pichenettes/ambika/voicecard/resources.h

// Copyright 2011 Emilie Gillet.
//
// Author: Emilie Gillet (emilie.o.gillet@gmail.com)
//
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
// -----------------------------------------------------------------------------
//
// Resources definitions.
//
// Automatically generated with:
// make resources


#ifndef VOICECARD_RESOURCES_H_
#define VOICECARD_RESOURCES_H_


#include "avrlib/base.h"

#include <avr/pgmspace.h>


#include "avrlib/resources_manager.h"

namespace ambika {

typedef uint8_t ResourceId;

extern const prog_char* const string_table[];

extern const prog_uint16_t* const lookup_table_table[];

extern const prog_uint8_t* const waveform_table[];

extern const prog_uint16_t lut_res_lfo_increments[] PROGMEM;
extern const prog_uint16_t lut_res_env_portamento_increments[] PROGMEM;
extern const prog_uint16_t lut_res_oscillator_increments[] PROGMEM;
extern const prog_uint16_t lut_res_fm_frequency_ratios[] PROGMEM;
extern const prog_uint16_t lut_res_vca_linearization[] PROGMEM;
extern const prog_uint16_t lut_res_cz_phase_reset[] PROGMEM;
extern const prog_uint8_t wav_res_formant_sine[] PROGMEM;
extern const prog_uint8_t wav_res_formant_square[] PROGMEM;
extern const prog_uint8_t wav_res_sine[] PROGMEM;
extern const prog_uint8_t wav_res_bandlimited_square_0[] PROGMEM;
extern const prog_uint8_t wav_res_bandlimited_square_1[] PROGMEM;
extern const prog_uint8_t wav_res_bandlimited_square_2[] PROGMEM;
extern const prog_uint8_t wav_res_bandlimited_square_3[] PROGMEM;
extern const prog_uint8_t wav_res_bandlimited_square_4[] PROGMEM;
extern const prog_uint8_t wav_res_bandlimited_square_5[] PROGMEM;
extern const prog_uint8_t wav_res_bandlimited_saw_0[] PROGMEM;
extern const prog_uint8_t wav_res_bandlimited_saw_1[] PROGMEM;
extern const prog_uint8_t wav_res_bandlimited_saw_2[] PROGMEM;
extern const prog_uint8_t wav_res_bandlimited_saw_3[] PROGMEM;
extern const prog_uint8_t wav_res_bandlimited_saw_4[] PROGMEM;
extern const prog_uint8_t wav_res_bandlimited_saw_5[] PROGMEM;
extern const prog_uint8_t wav_res_bandlimited_triangle_0[] PROGMEM;
extern const prog_uint8_t wav_res_bandlimited_triangle_3[] PROGMEM;
extern const prog_uint8_t wav_res_bandlimited_triangle_4[] PROGMEM;
extern const prog_uint8_t wav_res_bandlimited_triangle_5[] PROGMEM;
extern const prog_uint8_t wav_res_vowel_data[] PROGMEM;
extern const prog_uint8_t wav_res_distortion[] PROGMEM;
extern const prog_uint8_t wav_res_lfo_waveforms[] PROGMEM;
extern const prog_uint8_t wav_res_env_expo[] PROGMEM;
extern const prog_uint8_t wav_res_waves[] PROGMEM;
extern const prog_uint8_t wav_res_wavetables[] PROGMEM;
#define STR_RES_DUMMY 0  // dummy
#define LUT_RES_LFO_INCREMENTS 0
#define LUT_RES_LFO_INCREMENTS_SIZE 128
#define LUT_RES_ENV_PORTAMENTO_INCREMENTS 1
#define LUT_RES_ENV_PORTAMENTO_INCREMENTS_SIZE 128
#define LUT_RES_OSCILLATOR_INCREMENTS 2
#define LUT_RES_OSCILLATOR_INCREMENTS_SIZE 768
#define LUT_RES_FM_FREQUENCY_RATIOS 3
#define LUT_RES_FM_FREQUENCY_RATIOS_SIZE 25
#define LUT_RES_VCA_LINEARIZATION 4
#define LUT_RES_VCA_LINEARIZATION_SIZE 256
#define LUT_RES_CZ_PHASE_RESET 5
#define LUT_RES_CZ_PHASE_RESET_SIZE 4
#define WAV_RES_FORMANT_SINE 0
#define WAV_RES_FORMANT_SINE_SIZE 256
#define WAV_RES_FORMANT_SQUARE 1
#define WAV_RES_FORMANT_SQUARE_SIZE 256
#define WAV_RES_SINE 2
#define WAV_RES_SINE_SIZE 257
#define WAV_RES_BANDLIMITED_SQUARE_0 3
#define WAV_RES_BANDLIMITED_SQUARE_0_SIZE 257
#define WAV_RES_BANDLIMITED_SQUARE_1 4
#define WAV_RES_BANDLIMITED_SQUARE_1_SIZE 257
#define WAV_RES_BANDLIMITED_SQUARE_2 5
#define WAV_RES_BANDLIMITED_SQUARE_2_SIZE 257
#define WAV_RES_BANDLIMITED_SQUARE_3 6
#define WAV_RES_BANDLIMITED_SQUARE_3_SIZE 257
#define WAV_RES_BANDLIMITED_SQUARE_4 7
#define WAV_RES_BANDLIMITED_SQUARE_4_SIZE 257
#define WAV_RES_BANDLIMITED_SQUARE_5 8
#define WAV_RES_BANDLIMITED_SQUARE_5_SIZE 257
#define WAV_RES_BANDLIMITED_SQUARE_6 9
#define WAV_RES_BANDLIMITED_SQUARE_6_SIZE 257
#define WAV_RES_BANDLIMITED_SAW_0 10
#define WAV_RES_BANDLIMITED_SAW_0_SIZE 257
#define WAV_RES_BANDLIMITED_SAW_1 11
#define WAV_RES_BANDLIMITED_SAW_1_SIZE 257
#define WAV_RES_BANDLIMITED_SAW_2 12
#define WAV_RES_BANDLIMITED_SAW_2_SIZE 257
#define WAV_RES_BANDLIMITED_SAW_3 13
#define WAV_RES_BANDLIMITED_SAW_3_SIZE 257
#define WAV_RES_BANDLIMITED_SAW_4 14
#define WAV_RES_BANDLIMITED_SAW_4_SIZE 257
#define WAV_RES_BANDLIMITED_SAW_5 15
#define WAV_RES_BANDLIMITED_SAW_5_SIZE 257
#define WAV_RES_BANDLIMITED_SAW_6 16
#define WAV_RES_BANDLIMITED_SAW_6_SIZE 257
#define WAV_RES_BANDLIMITED_TRIANGLE_0 17
#define WAV_RES_BANDLIMITED_TRIANGLE_0_SIZE 257
#define WAV_RES__BANDLIMITED_TRIANGLE_0 18
#define WAV_RES__BANDLIMITED_TRIANGLE_0_SIZE 257
#define WAV_RES___BANDLIMITED_TRIANGLE_0 19
#define WAV_RES___BANDLIMITED_TRIANGLE_0_SIZE 257
#define WAV_RES_BANDLIMITED_TRIANGLE_3 20
#define WAV_RES_BANDLIMITED_TRIANGLE_3_SIZE 257
#define WAV_RES_BANDLIMITED_TRIANGLE_4 21
#define WAV_RES_BANDLIMITED_TRIANGLE_4_SIZE 257
#define WAV_RES_BANDLIMITED_TRIANGLE_5 22
#define WAV_RES_BANDLIMITED_TRIANGLE_5_SIZE 257
#define WAV_RES_BANDLIMITED_TRIANGLE_6 23
#define WAV_RES_BANDLIMITED_TRIANGLE_6_SIZE 257
#define WAV_RES_VOWEL_DATA 24
#define WAV_RES_VOWEL_DATA_SIZE 63
#define WAV_RES_DISTORTION 25
#define WAV_RES_DISTORTION_SIZE 256
#define WAV_RES_LFO_WAVEFORMS 26
#define WAV_RES_LFO_WAVEFORMS_SIZE 2
#define WAV_RES_ENV_EXPO 27
#define WAV_RES_ENV_EXPO_SIZE 257
#define WAV_RES_WAVES 28
#define WAV_RES_WAVES_SIZE 10320
#define WAV_RES_WAVETABLES 29
#define WAV_RES_WAVETABLES_SIZE 288
typedef avrlib::ResourcesManager<
    ResourceId,
    avrlib::ResourcesTables<
        string_table,
        lookup_table_table> > ResourcesManager; 

}  // namespace ambika

#endif  // VOICECARD_RESOURCES_H_
