pichenettes/ambika/controller/multi.h

// Copyright 2011 Emilie Gillet.
//
// Author: Emilie Gillet (emilie.o.gillet@gmail.com)
//
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
// -----------------------------------------------------------------------------
//
// "MultiData" is the dumb data structure storing the global settings.
// "Multi" is the root synthesis engine.

#ifndef CONTROLLER_MULTI_H_
#define CONTROLLER_MULTI_H_

#include "avrlib/base.h"

#include "controller/controller.h"
#include "controller/part.h"

namespace ambika {
  
struct KnobAssignment {
  uint8_t part;
  uint8_t parameter;
  uint8_t instance;
};

struct PartMapping {
  uint8_t midi_channel;
  uint8_t keyrange_low;
  uint8_t keyrange_high;
  uint8_t voice_allocation;
  
  inline uint8_t receive_channel(uint8_t channel) const {
    return !midi_channel || (channel + 1 == midi_channel);
  }
  
  inline uint8_t accept_note(uint8_t note) const {
    if (keyrange_low <= keyrange_high) {
      return (note >= keyrange_low && note <= keyrange_high);
    } else {
      return note <= keyrange_high || note >= keyrange_low;
    }
  }
  
  inline uint8_t accept_channel_note(uint8_t channel, uint8_t note) const {
    return receive_channel(channel) && accept_note(note);
  }
  
  inline uint8_t tx_channel() const {
    return midi_channel == 0 ? 0 : midi_channel - 1;
  }
};

struct MultiData {
  // Offset: 0-24
  PartMapping part_mapping_[kNumParts];
  
  // Offset: 24-28
  uint8_t clock_bpm;
  uint8_t clock_groove_template;
  uint8_t clock_groove_amount;
  uint8_t clock_release;
  
  // Offset: 28-52
  KnobAssignment knob_assignment[8];
  
  // Offset: 52-56
  uint8_t padding2[4];
};

typedef MultiData PROGMEM prog_MultiData;

enum MultiParameter {
  PRM_MULTI_MIDI_CHANNEL,
  PRM_MULTI_KEYRANGE_LOW,
  PRM_MULTI_KEYRANGE_HIGH,
  PRM_MULTI_VOICE_ALLOCATION,
  
  PRM_MULTI_CLOCK_BPM = 24,
  PRM_MULTI_CLOCK_GROOVE_TEMPLATE = 25,
  PRM_MULTI_CLOCK_GROOVE_AMOUNT = 26,
  PRM_MULTI_CLOCK_LATCH = 27,
};

static const uint8_t kNumStepsInGroovePattern = 16;
static const uint8_t kNumTicksPerStep = 6;

class Multi {
 public:
  Multi() { }
  static void Init(bool force_reset);
  
  static void InitSettings(InitializationMode mode);
  
  static void StartNote(uint8_t note) {
    if (!running_) {
      Start();
    }
    for (uint8_t i = 0; i < kNumParts; ++i) {
      parts_[i].NoteOn(note, 0x64);
    }
  }
  
  static void StopNote(uint8_t note) {
    for (uint8_t i = 0; i < kNumParts; ++i) {
      parts_[i].NoteOff(note);
    }
  }
  
  static void NoteOn(uint8_t channel, uint8_t note, uint8_t velocity) {
    // If no note has been played for a while, reset the sequencer and
    // arpeggiator to the first step.
    if (!running_) {
      Start();
    }
    for (uint8_t i = 0; i < kNumParts; ++i) {
      if (data_.part_mapping_[i].accept_channel_note(channel, note)) {
        parts_[i].NoteOn(note, velocity);
      }
    }
  }
  static void NoteOff(uint8_t channel, uint8_t note, uint8_t velocity) {
    for (uint8_t i = 0; i < kNumParts; ++i) {
      if (data_.part_mapping_[i].accept_channel_note(channel, note)) {
        parts_[i].NoteOff(note);
      }
    }
  }
  static void ControlChange(
      uint8_t channel,
      uint8_t controller,
      uint8_t value) {
    for (uint8_t i = 0; i < kNumParts; ++i) {
      if (data_.part_mapping_[i].receive_channel(channel)) {
        parts_[i].ControlChange(controller, value);
      }
    }
  }
  static void PitchBend(uint8_t channel, uint16_t pitch_bend) {
    for (uint8_t i = 0; i < kNumParts; ++i) {
      if (data_.part_mapping_[i].receive_channel(channel)) {
        parts_[i].PitchBend(pitch_bend);
      }
    }
  }
  static void Aftertouch(uint8_t channel, uint8_t note, uint8_t velocity) {
    for (uint8_t i = 0; i < kNumParts; ++i) {
      if (data_.part_mapping_[i].accept_channel_note(channel, note)) {
        parts_[i].Aftertouch(note, velocity);
      }
    }
  }
  static void Aftertouch(uint8_t channel, uint8_t velocity) {
    for (uint8_t i = 0; i < kNumParts; ++i) {
      if (data_.part_mapping_[i].receive_channel(channel)) {
        parts_[i].Aftertouch(velocity);
      }
    }
  }
  static void AllSoundOff(uint8_t channel) {
    for (uint8_t i = 0; i < kNumParts; ++i) {
      if (data_.part_mapping_[i].receive_channel(channel)) {
        parts_[i].AllSoundOff();
      }
    }
  }
  static void ResetAllControllers(uint8_t channel) {
    for (uint8_t i = 0; i < kNumParts; ++i) {
      if (data_.part_mapping_[i].receive_channel(channel)) {
        parts_[i].ResetAllControllers();
      }
    }
  }
  static void AllNotesOff(uint8_t channel) {
    for (uint8_t i = 0; i < kNumParts; ++i) {
      if (data_.part_mapping_[i].receive_channel(channel)) {
        parts_[i].AllNotesOff();
      }
    }
  }
  static void OmniModeOff(uint8_t channel) {
    for (uint8_t i = 0; i < kNumParts; ++i) {
      if (data_.part_mapping_[i].receive_channel(channel)) {
        data_.part_mapping_[i].midi_channel = channel + 1;
      }
    }
  }
  static void OmniModeOn(uint8_t channel) {
    for (uint8_t i = 0; i < kNumParts; ++i) {
      if (data_.part_mapping_[i].receive_channel(channel)) {
        data_.part_mapping_[i].midi_channel = 0;
      }
    }
  }
  static void MonoModeOn(uint8_t channel, uint8_t num_channels) {
    for (uint8_t i = 0; i < kNumParts; ++i) {
      if (data_.part_mapping_[i].receive_channel(channel)) {
        parts_[i].MonoModeOn(num_channels);
      }
    }
  }
  static void PolyModeOn(uint8_t channel) {
    for (uint8_t i = 0; i < kNumParts; ++i) {
      if (data_.part_mapping_[i].receive_channel(channel)) {
        parts_[i].PolyModeOn();
      }
    }
  }
  static void Reset() {
    for (uint8_t i = 0; i < kNumParts; ++i) {
      parts_[i].Reset();
    }
  }
  static void Clock();
  static void Start();
  static void Stop();
  static void Continue() {
    Start();
  }
  
  static void Tick() {
    ++clock_counter_;
    ++lfo_refresh_counter_;
    if (clock_counter_ >= tick_duration_) {
      ++num_clock_events_;
      clock_counter_ = 0;
    }
  }
  
  static void SetValue(uint8_t address, uint8_t value);
  static inline uint8_t GetValue(uint8_t address) {
    uint8_t* bytes = static_cast<uint8_t*>(static_cast<void*>(&data_));
    return bytes[address];
  }
  
  static void UpdateClocks();
  
  static Part* mutable_part(uint8_t i) { return &parts_[i]; }
  static const Part& part(uint8_t i) { return parts_[i]; }
  
  static MultiData* mutable_data() { return &data_; }
  static const MultiData& data() { return data_; }
  static const uint8_t* raw_data() {
    return static_cast<const uint8_t*>(static_cast<const void*>(&data_));
  }
  static uint8_t* mutable_raw_data() { 
    return static_cast<uint8_t*>(static_cast<void*>(&data_));
  }
  
  static uint8_t internal_clock() { return data_.clock_bpm >= 40; }

  static uint8_t SolveAllocationConflicts(uint8_t constraint);
  static void AssignVoicesToParts();
  
  static uint8_t part_channel(Part* part) {
    for (uint8_t i = 0; i < kNumParts; ++i) {
      if (&parts_[i] == part) {
        return data_.part_mapping_[i].tx_channel();
      }
    }
    return 0;
  }
  
  static uint8_t step() { return step_count_; }
  static uint8_t running() { return running_; }
  static void Touch();
  
  static inline uint8_t flags() {
    uint8_t result = flags_;
    for (uint8_t i = 0; i < kNumParts; ++i) {
      result |= parts_[i].flags();
    }
    return result;
  }
  
  inline void ClearFlag(uint8_t flag) {
    flags_ &= ~flag;
    for (uint8_t i = 0; i < kNumParts; ++i) {
      parts_[i].ClearFlag(flag);
    }
  }
  
 private:
  static void ComputeInternalClockOverflowsTable();
  
  // Incremented at 39kHz
  static uint16_t clock_counter_;
  static uint16_t lfo_refresh_counter_;
  // Incremented at 39kHz / 40
  static uint8_t lfo_refresh_cycle_;
  static volatile uint8_t num_clock_events_;

  // Duration of a clock tick, in 39kHz increments.
  static uint16_t tick_duration_;
  // Incremented at each clock tick, reset after 6 ticks.
  static uint8_t tick_count_;
  // Incremented every 6 tick.
  static uint8_t step_count_;
  // Incremented at each clock tick if no key is pressed.
  static uint8_t idle_ticks_;
  // Whether the clock is started.
  static uint8_t running_;
  // This list of tick durations is computed from the BPM and the groove
  // template.
  static uint16_t tick_duration_table_[kNumStepsInGroovePattern];
  

  static MultiData data_;
  static Part parts_[kNumParts];
  static uint8_t flags_;
  
  DISALLOW_COPY_AND_ASSIGN(Multi);
};

extern Multi multi;

}  // namespace ambika

#endif  // CONTROLLER_MULTI_H_
