pichenettes/ambika/controller/storage.cc

// Copyright 2011 Emilie Gillet.
//
// Author: Emilie Gillet (emilie.o.gillet@gmail.com)
//
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
// -----------------------------------------------------------------------------
//
// Patch storage and SysEx transfer.

#include "controller/storage.h"

#include <avr/eeprom.h>

#include "avrlib/op.h"
#include "avrlib/string.h"

#include "controller/display.h"
#include "controller/midi_dispatcher.h"
#include "controller/multi.h"
#include "controller/system_settings.h"
#include "controller/ui.h"

namespace ambika {


static const uint32_t kRiffTag = FourCC<'R', 'I', 'F', 'F'>::value;
static const uint32_t kFormatTag = FourCC<'M', 'B', 'K', 'S'>::value;
static const uint32_t kNameTag = FourCC<'n', 'a', 'm', 'e'>::value;
static const uint32_t kObjectTag = FourCC<'o', 'b', 'j', ' '>::value;

using namespace avrlib;

static const prog_char sysex_header[] PROGMEM = {
  0xf0,  // <SysEx>
  0x00, 0x21, 0x02,  // Mutable instruments manufacturer id.
  0x00, 0x04,  // Product ID for Ambika-6.
};

/* static */
Filesystem Storage::fs_;

/* static */
File Storage::file_;

/* static */
uint8_t* Storage::buffer_;

/* static */
uint16_t Storage::sysex_rx_bytes_received_;

/* static */
uint8_t Storage::sysex_rx_checksum_;

/* static */
uint8_t Storage::sysex_rx_state_;

/* static */
uint16_t Storage::sysex_rx_expected_size_;

/* static */
uint8_t Storage::sysex_rx_command_[2];

/* static */
char Storage::tmp_buffer_[64];

/* static */
uint8_t Storage::version_[kNumVoices * 3 + 1];

/* static */
void Storage::Init() {
  buffer_ = fs_.buffer();
}

/* static */
uint8_t Storage::Checksum(const void* data, uint8_t size) {
  uint8_t s = 0;
  const uint8_t* d = static_cast<const uint8_t*>(data);
  while (size--) {
    s += *d++;
  }
  return s;
}

/* static */
void Storage::WriteMultiToEeprom() {
  uint16_t address = 0;
  for (uint8_t i = 0; i < kNumParts; ++i) {
    EepromWrite(
        multi.part(i).raw_data(),
        sizeof(PartData),
        &address);
    EepromWrite(
        multi.part(i).raw_patch_data(),
        sizeof(Patch),
        &address);
  }
  EepromWrite(multi.raw_data(), sizeof(MultiData), &address);
}

/* static */
uint8_t Storage::LoadMultiFromEeprom() {
  uint16_t address = 0;
  uint8_t success = 1;
  for (uint8_t i = 0; i < kNumParts; ++i) {
    success = success && Storage::EepromRead(
        multi.mutable_part(i)->mutable_raw_data(),
        sizeof(PartData),
        &address);
    success = success && Storage::EepromRead(
        multi.mutable_part(i)->mutable_raw_patch_data(),
        sizeof(Patch),
        &address);
  }
  success = success && Storage::EepromRead(
      multi.mutable_raw_data(),
      sizeof(MultiData),
      &address);
  return success;
}


/* static */
void Storage::EepromWrite(const void* data, uint8_t size, uint16_t* offset) {
  eeprom_write_block(const_cast<void*>(data), (void*)(*offset), size);
  *offset += size;
  eeprom_write_byte((uint8_t*)(*offset), Storage::Checksum(data, size));
  *offset += 1;
}

/* static */
uint8_t Storage::EepromRead(
    void* data,
    uint8_t size,
    uint16_t* offset) {
  eeprom_read_block(data, (void*)(*offset), size);
  *offset += size;
  uint8_t expected_checksum = eeprom_read_byte((uint8_t*)(*offset));
  *offset += 1;
  return Storage::Checksum(data, size) == expected_checksum;
}

/* static */
uint8_t Storage::object_size(const StorageLocation& location) {
  switch (location.object) {
    case STORAGE_OBJECT_PATCH:
      return sizeof(Patch);
      
    case STORAGE_OBJECT_SEQUENCE:
      return 72;
      
    case STORAGE_OBJECT_PART:
      return sizeof(PartData);
      
    case STORAGE_OBJECT_MULTI:
      return sizeof(MultiData);
  }
  return 0;
}

/* static */
uint16_t Storage::riff_size(const StorageLocation& location) {
  switch (location.object) {
    case STORAGE_OBJECT_MULTI:
      return (sizeof(Patch) + 12 + sizeof(PartData) + 12) * kNumParts + \
          sizeof(MultiData) + 12;

    case STORAGE_OBJECT_PROGRAM:
      return sizeof(Patch) + 12 + sizeof(PartData) + 12;
    
    default:
      return object_size(location) + 12;
  }
  return 0;
}

/* static */
const uint8_t* Storage::object_data(const StorageLocation& location) {
  switch (location.object) {
    case STORAGE_OBJECT_PATCH:
      return multi.part(location.part).raw_patch_data();
      
    case STORAGE_OBJECT_SEQUENCE:
      return multi.part(location.part).raw_sequence_data();
      
    case STORAGE_OBJECT_PART:
      return multi.part(location.part).raw_data();
      
    case STORAGE_OBJECT_MULTI:
      return multi.raw_data();
  }
  return NULL;
}

/* static */
uint8_t* Storage::mutable_object_data(const StorageLocation& location) {
  switch (location.object) {
    case STORAGE_OBJECT_PATCH:
      return multi.mutable_part(location.part)->mutable_raw_patch_data();
      
    case STORAGE_OBJECT_SEQUENCE:
      return multi.mutable_part(location.part)->mutable_raw_sequence_data();
      
    case STORAGE_OBJECT_PART:
      return multi.mutable_part(location.part)->mutable_raw_data();
      
    case STORAGE_OBJECT_MULTI:
      return multi.mutable_raw_data();
  }
  return NULL;
}

/* static */
uint8_t Storage::has_user_changes(const StorageLocation& location) {
  if (location.object == STORAGE_OBJECT_MULTI) {
    return multi.flags() & FLAG_HAS_USER_CHANGE;
  } else {
    return multi.part(location.part).flags() & FLAG_HAS_USER_CHANGE;
  }
}

/* static */
FilesystemStatus Storage::Snapshot(const StorageLocation& location) {
  StorageLocation l = location;
  uint8_t version = version_[location.index()];
  l.slot = version;
  Save(STORAGE_HISTORY, l);
  
  // Create a gap in the version number sequence to prevent forwarding.
  ++version;
  l.slot = version;
  char* forward_version_name = GetFileName(STORAGE_HISTORY, l);
  {
    scoped_resource<SdCardSession> session;
    InvalidatePendingSysExTransfer();
    fs_.Unlink(forward_version_name);
  }
  version_[location.index()] = version;
}

/* static */
FilesystemStatus Storage::PreviousVersion(const StorageLocation& location) {
  StorageLocation l = location;
  uint8_t version = version_[location.index()] - 1;
  l.slot = version;
  FilesystemStatus status = Load(STORAGE_HISTORY, l, 1);
  if (status == FS_OK) {
    version_[location.index()] = version;
  }
  return status;
}

/* static */
FilesystemStatus Storage::NextVersion(const StorageLocation& location) {
  StorageLocation l = location;
  uint8_t version = version_[location.index()] + 1;
  l.slot = version;
  FilesystemStatus status = Load(STORAGE_HISTORY, l, 1);
  if (status == FS_OK) {
    version_[location.index()] = version;
  }
  return status;
}

/* static */
void Storage::ForEachObject(
    const StorageLocation& location,
    ObjectFn object_fn) {
  StorageLocation destination = location;
  destination.alias = 0;
  switch(destination.object) {
    case STORAGE_OBJECT_PATCH:
    case STORAGE_OBJECT_SEQUENCE:
    case STORAGE_OBJECT_PART:
      (*object_fn)(destination);
      break;
      
    case STORAGE_OBJECT_PROGRAM:
      destination.object = STORAGE_OBJECT_PATCH;
      (*object_fn)(destination);
      destination.object = STORAGE_OBJECT_PART;
      (*object_fn)(destination);
      break;
      
    case STORAGE_OBJECT_MULTI:
      (*object_fn)(destination);
      for (uint8_t i = 0; i < kNumParts; ++i) {
        destination.part = i;
        destination.alias = i + 1;
        destination.object = STORAGE_OBJECT_PATCH;
        (*object_fn)(destination);
        destination.object = STORAGE_OBJECT_PART;
        (*object_fn)(destination);
      }
      break;
  }
}

/* static */
void Storage::ReadObject(const StorageLocation& location) {
  uint8_t* data = mutable_object_data(location);
  uint8_t size = object_size(location);
  if (size) {
    memcpy(data, buffer_, size);
  }
}

/* static */
void Storage::TouchObject(const StorageLocation& location) {
  // Recompute the dependent variables and update the voicecard. Mark that the
  // object is freshly loaded and has received no user changes.
  switch (location.object) {
    case STORAGE_OBJECT_PATCH:
      multi.mutable_part(location.part)->TouchPatch();
      break;

    case STORAGE_OBJECT_PART:
    case STORAGE_OBJECT_SEQUENCE:
      multi.mutable_part(location.part)->Touch();
      break;
    
    case STORAGE_OBJECT_MULTI:
      multi.Touch();
      break;
  }
}

/* static */
void Storage::SysExSendObject(const StorageLocation& location) {
  SysExSendRaw(
      location.object + 1,
      location.alias,
      object_data(location),
      object_size(location),
      false);
}

/* static */
void Storage::SysExSendRaw(
    uint8_t command,
    uint8_t argument,
    const uint8_t* data,
    uint8_t size,
    bool send_address) {
  midi_dispatcher.Flush();
  for (uint8_t i = 0; i < sizeof(sysex_header); ++i) {
    midi_dispatcher.SendBlocking(pgm_read_byte(sysex_header + i));
  }
  midi_dispatcher.SendBlocking(command);
  midi_dispatcher.SendBlocking(argument);
  // Outputs the data.
  uint8_t checksum = 0;
  if (send_address) {
    Word address;
    address.value = (uint16_t)(void*)(data);
    checksum += address.bytes[0];
    checksum += address.bytes[1];
    midi_dispatcher.SendBlocking(U8ShiftRight4(address.bytes[0]));
    midi_dispatcher.SendBlocking(address.bytes[0] & 0x0f);
    midi_dispatcher.SendBlocking(U8ShiftRight4(address.bytes[1]));
    midi_dispatcher.SendBlocking(address.bytes[1] & 0x0f);
  }
  for (uint8_t i = 0; i < size; ++i) {
    checksum += data[i];
    midi_dispatcher.SendBlocking(U8ShiftRight4(data[i]));
    midi_dispatcher.SendBlocking(data[i] & 0x0f);
  }
  // Outputs a checksum.
  midi_dispatcher.SendBlocking(U8ShiftRight4(checksum));
  midi_dispatcher.SendBlocking(checksum & 0x0f);

  // End of SysEx block.
  midi_dispatcher.SendBlocking(0xf7);
  midi_dispatcher.Flush();
}

/* static */
void Storage::RIFFWriteObject(const StorageLocation& location) {
  const uint8_t* data = object_data(location);
  uint8_t size = object_size(location);
  
  LongWord w;
  uint16_t written;

  // Write the RIFF header.
  w.value = kObjectTag;
  file_.Write(w.bytes, 4, &written);
  w.value = size + 4;
  file_.Write(w.bytes, 4, &written);
  // Write the position words.
  w.value = 0;
  w.bytes[0] = location.object + 1;
  w.bytes[1] = location.alias;
  file_.Write(w.bytes, 4, &written);
  
  // Write the data.
  file_.Write(data, size, &written);
}

/* static */
FilesystemStatus Storage::Load(
    StorageDir type,
    const StorageLocation& location,
    uint8_t load_contents) {
  {
    scoped_resource<SdCardSession> session;

    FilesystemStatus s;
    char* name = GetFileName(type, location);
  
    file_.Close();
    InvalidatePendingSysExTransfer();
  
    s = file_.Open(name, FA_READ | FA_OPEN_EXISTING, kFsInitTimeout);
    if (s != FS_OK) {
      return s;
    }
  
    LongWord id;
    LongWord size;
    uint16_t read;
  
    file_.Read(id.bytes, 4, &read);
    if (id.value != kRiffTag) {
      file_.Close();
      return FS_BAD_FILE_FORMAT;
    }
    // Skip the size.
    file_.Read(size.bytes, 4, &read);
    file_.Read(id.bytes, 4, &read);
    if (id.value != kFormatTag) {
      file_.Close();
      return FS_BAD_FILE_FORMAT;
    }
  
    while (!file_.eof()) {
      file_.Read(id.bytes, 4, &read);
      file_.Read(size.bytes, 4, &read);
      uint8_t skip_data = 1;
    
      if (id.value == kObjectTag && load_contents) {
        file_.Read(id.bytes, 4, &read);
        StorageLocation destination;
        destination.object = static_cast<StorageObject>(id.bytes[0] - 1);
        destination.part = id.bytes[1] == 0 ? location.part : (id.bytes[1] - 1);
      
        uint8_t expected_size = object_size(destination);
        if (expected_size == size.value - 4) {
          uint8_t* data = mutable_object_data(destination);
          file_.Read(data, expected_size, &read);
          skip_data = 0;
        }
      } else if (id.value == kNameTag && location.name) {
        file_.Read(location.name, size.value, &read);
        skip_data = 0;
      }
      if (skip_data) {
        file_.Seek(file_.tell() + size.value);
      }
    }

    file_.Close();
  }
  
  // Refresh all datastructures.
  if (load_contents) {
    ForEachObject(location, TouchObject);
  }

  return FS_OK;
}

/* static */
FilesystemStatus Storage::Save(
    StorageDir type,
    const StorageLocation& location) {
  scoped_resource<SdCardSession> session;
  
  FilesystemStatus s;
  char* name = GetFileName(type, location);

  file_.Close();
  InvalidatePendingSysExTransfer();
  
  // Create a backup of the older version.
  if (type == STORAGE_CLIPBOARD ||
      (type == STORAGE_BANK && system_settings.data().autobackup)) {
    char* backup_name = tmp_buffer_ + 32;
    strcpy(backup_name, name);
    backup_name[strlen(backup_name) - 3] = '~';
    
    // Remove the old backup.
    fs_.Unlink(backup_name);
    
    // Rename current version with the backup name.
    fs_.Rename(name, backup_name);
  }
  
  // Attempt to open.
  s = file_.Open(name, FA_WRITE | FA_CREATE_ALWAYS, kFsInitTimeout);
  if (s == FS_PATH_NOT_FOUND) {
    fs_.Mkdirs(name);
    s = file_.Open(name, FA_WRITE | FA_CREATE_ALWAYS, kFsInitTimeout);
  }
  
  // There's nothing we can do if Open failed at this stage.
  if (s != FS_OK) {
    return s;
  }
  
  LongWord w;
  uint16_t written;
  
  // RIFF header.
  w.value = kRiffTag;
  file_.Write(w.bytes, 4, &written);
  w.value = 4 + 24 + riff_size(location);
  file_.Write(w.bytes, 4, &written);
  w.value = kFormatTag;
  file_.Write(w.bytes, 4, &written);
  
  // NAME block.
  w.value = kNameTag;
  file_.Write(w.bytes, 4, &written);
  w.value = 16;
  file_.Write(w.bytes, 4, &written);
  file_.Write(location.name, 16, &written);

  // Write subchunks.
  ForEachObject(location, &RIFFWriteObject);
  
  file_.Close();
  return FS_OK;
}

/* static */
char* Storage::GetFileName(StorageDir type, const StorageLocation& location) {
  char* p = tmp_buffer_;

  // Root.
  *p++ = '/';

  // Object name.
  ResourcesManager::LoadStringResource(STR_RES_PATCH + location.object, p, 32);
  p += strlen(p);
  
  // Path.
  if (type == STORAGE_CLIPBOARD || type == STORAGE_PREVIOUS_CLIPBOARD) {
    strcat_P(p, PSTR("/CLIPBRD/CLIPBRD"));
    p += strlen(p);
  } else if (type == STORAGE_HISTORY) {
    strcat_P(p, PSTR("/HISTORY/"));
    p += strlen(p);
    if (location.object != STORAGE_OBJECT_MULTI) {
      *p++ = '0' + (location.part);
      *p++ = '/';
    }
  } else if (type == STORAGE_BANK) {
    strcat_P(p, PSTR("/BANK/"));
    p += strlen(p);
    *p++ = 'A' + (location.bank);
    *p++ = '/';
  }
  
  // Name.
  if (type != STORAGE_CLIPBOARD && type != STORAGE_PREVIOUS_CLIPBOARD) {
    UnsafeItoa<int16_t>(location.slot, 3, p);
    PadRight(p, 3, '0');
    p += 3;
  }
  
  // Extension dot.
  *p++ = '.';
  
  // Extension name.
  ResourcesManager::LoadStringResource(STR_RES_PATCH + location.object, p, 3);
  p += 3;
  
  if (type == STORAGE_PREVIOUS_CLIPBOARD) {
    p[-3] = '~';
  }
  *p = '\0';
  
  return tmp_buffer_;
}

/* static */
void Storage::Expand(const prog_char* name, char variable) {
  strcpy_P(tmp_buffer_, name);
  for (uint8_t i = 0; i < sizeof(tmp_buffer_); ++i) {
    if (tmp_buffer_[i] == '$') {
      tmp_buffer_[i] = variable;
    }
  }
}

/* static */
FilesystemStatus Storage::SpiCopy(
    uint8_t voice_id,
    const prog_char* name,
    char variable,
    uint8_t page_size_nibbles) {
  scoped_resource<SdCardSession> session;
  file_.Close();
  InvalidatePendingSysExTransfer();
  
  FilesystemStatus s;
  Expand(name, variable);
  s = file_.Open(tmp_buffer_, FA_READ | FA_OPEN_EXISTING, kFsInitTimeout);
  if (s != FS_OK) {
    return s;
  }
  uint8_t bytes[4];
  uint16_t page_count = 0;
  uint16_t page_size = U8U8Mul(page_size_nibbles, 16);
  uint8_t byte_count = 0;
  while (!file_.eof()) {
    uint16_t read;

    // Read a few bytes.
    {
      scoped_resource<SdCardSession> session;
      s = file_.Read(bytes, 4, &read);
    }
    for (uint8_t i = 0; i < read; ++i) {
      if (voicecard_tx.WriteAsNibbles(voice_id, bytes[i]) != byte_count) {
        return FS_COPY_ERROR;
      }
      ++page_count;
      ++byte_count;
    }
    // Pause every time a page is full to let the voicecard write its
    // input buffer to the flash.
    if (page_count == page_size) {
      ConstantDelay(15);
      page_count = 0;
    }
  }
  file_.Close();
  return s;
}

/* static */
uint8_t Storage::FileExists(const prog_char* name, char variable) {
  scoped_resource<SdCardSession> session;

  file_.Close();
  InvalidatePendingSysExTransfer();
  
  FilesystemStatus s;
  Expand(name, variable);
  s = file_.Open(tmp_buffer_, FA_READ | FA_OPEN_EXISTING, kFsInitTimeout);
  file_.Close();
  return (s == FS_OK);
}


/* static */
void Storage::SysExParseCommand() {
  sysex_rx_bytes_received_ = 0;
  sysex_rx_state_ = RECEIVING_DATA;
  switch (sysex_rx_command_[0]) {
    case 0x01:
    case 0x02:
    case 0x03:
    case 0x04:
    case 0x05:
      {
        StorageLocation location;
        location.object = static_cast<StorageObject>(sysex_rx_command_[0] - 1);
        sysex_rx_expected_size_ = object_size(location);
      }
      break;
      
    case 0x0f:
      // POKE command contains 2 bytes of address + $argument bytes of data.
      {
        sysex_rx_expected_size_ = 2 + sysex_rx_command_[1];
      }
      break;

    case 0x11:
    case 0x12:
    case 0x13:
    case 0x14:
    case 0x15:
      // Request commands have no data.
      sysex_rx_expected_size_ = 0;
      break;
      
    case 0x1f:
      // PEEK command accepts 2 bytes (address).
      sysex_rx_expected_size_ = 2;
      break;
    
    default:
      sysex_rx_state_ = RECEIVING_FOOTER;
      break;
  }
}

/* static */
void Storage::SysExAcceptCommand() {
  uint8_t success = 1;
  
  StorageLocation location;
  location.part = sysex_rx_command_[1] == 0
    ?  ui.state().active_part
    : sysex_rx_command_[1] - 1;

  switch (sysex_rx_command_[0]) {
    case 0x01:
    case 0x02:
    case 0x03:
    case 0x04:
    case 0x05:
      location.object = static_cast<StorageObject>(sysex_rx_command_[0] - 0x01);
      ReadObject(location);
      TouchObject(location);
      break;

    case 0x0f:
      // POKE
      {
        Word address;
        address.bytes[0] = buffer_[0];
        address.bytes[1] = buffer_[1];
        uint8_t size = sysex_rx_command_[1];
        uint8_t* p = (uint8_t*)(address.value);
        memcpy(p, buffer_ + 2, size);
      }
      break;

    case 0x11:
    case 0x12:
    case 0x13:
    case 0x14:
    case 0x15:
      location.object = static_cast<StorageObject>(sysex_rx_command_[0] - 0x11);
      SysExSend(location);
      break;
      
    case 0x1f:
      // PEEK
      {
        Word address;
        address.bytes[0] = buffer_[0];
        address.bytes[1] = buffer_[1];
        uint8_t size = sysex_rx_command_[1];
        const uint8_t* p = (const uint8_t*)(address.value);
        SysExSendRaw(0x0f, size, p, size, true);
      }
      break;
      
    default:
      success = 0;
      break;
  }
  sysex_rx_state_ = success ? RECEPTION_OK : RECEPTION_ERROR;
}

/* static */
void Storage::SysExReceive(uint8_t byte) {
  if (byte == 0xf0) {
    sysex_rx_checksum_ = 0;
    sysex_rx_bytes_received_ = 0;
    sysex_rx_state_ = RECEIVING_HEADER;
  }
  
  switch (sysex_rx_state_) {
    case RECEIVING_HEADER:
      if (pgm_read_byte(sysex_header + sysex_rx_bytes_received_) == byte) {
        sysex_rx_bytes_received_++;
        if (sysex_rx_bytes_received_ >= sizeof(sysex_header)) {
          sysex_rx_state_ = RECEIVING_COMMAND;
          sysex_rx_bytes_received_ = 0;
        }
      } else {
        sysex_rx_state_ = RECEIVING_FOOTER;
      }
      break;

    case RECEIVING_COMMAND:
      sysex_rx_command_[sysex_rx_bytes_received_++] = byte;
      if (sysex_rx_bytes_received_ == 2) {
        SysExParseCommand();
      }
      break;

    case RECEIVING_DATA:
      {
        uint16_t i = sysex_rx_bytes_received_ >> 1;
        if (sysex_rx_bytes_received_ & 1) {
          buffer_[i] |= byte & 0xf;
          if (i < sysex_rx_expected_size_) {
            sysex_rx_checksum_ += buffer_[i];
          }
        } else {
          buffer_[i] = U8ShiftLeft4(byte);
        }
        sysex_rx_bytes_received_++;
        if (sysex_rx_bytes_received_ >= (1 + sysex_rx_expected_size_) * 2) {
          sysex_rx_state_ = RECEIVING_FOOTER;
        }
      }
    break;

  case RECEIVING_FOOTER:
    if (byte == 0xf7 &&
        sysex_rx_checksum_ == buffer_[sysex_rx_expected_size_] &&
        system_settings.rx_sysex()) {
      SysExAcceptCommand();
    } else {
      sysex_rx_state_ = RECEPTION_ERROR;
    }
    break;
  }
}

/* static */
void Storage::InvalidatePendingSysExTransfer() {
  sysex_rx_state_ = RECEPTION_ERROR;
}
  
/* extern */
Storage storage;

}  // namespace ambika
