pichenettes/ambika/voicecard/resources.cc

// Copyright 2011 Emilie Gillet.
//
// Author: Emilie Gillet (emilie.o.gillet@gmail.com)
//
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
// -----------------------------------------------------------------------------
//
// Resources definitions.
//
// Automatically generated with:
// make resources


#include "voicecard/resources.h"

namespace ambika {

static const prog_char str_res_dummy[] PROGMEM = "dummy";


PROGMEM const prog_char* const string_table[] = {
  str_res_dummy,
};

const prog_uint16_t lut_res_lfo_increments[] PROGMEM = {
       4,      4,      4,      4,      5,      5,      5,      6,
       6,      7,      7,      7,      8,      8,      9,      9,
      10,     11,     11,     12,     13,     14,     14,     15,
      16,     17,     18,     20,     21,     22,     23,     25,
      26,     28,     30,     31,     33,     35,     37,     40,
      42,     45,     47,     50,     53,     57,     60,     64,
      67,     71,     76,     80,     85,     90,     96,    101,
     108,    114,    121,    128,    136,    144,    153,    162,
     172,    182,    193,    204,    217,    230,    243,    258,
     273,    290,    307,    325,    345,    366,    388,    411,
     435,    461,    489,    518,    549,    582,    617,    654,
     693,    735,    779,    825,    875,    927,    982,   1041,
    1104,   1170,   1240,   1314,   1392,   1476,   1564,   1657,
    1757,   1862,   1973,   2091,   2216,   2349,   2489,   2638,
    2796,   2963,   3141,   3329,   3528,   3739,   3962,   4199,
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
      42,     43,     43,     44,     44,     44,     44,     44,
       0,      0,      0,      0,      0,      0,      0,      0,
       8,     73,     73,     69,     72,     72,     72,     72,
      72,     72,      0,      0,      0,      0,      0,      0,
       0,      0,     16,      3,     45,     45,     72,     46,
      46,     46,     47,     48,     48,     49,     50,     50,
      46,     51,     51,     51,     16,     13,      0,      1,
       2,      3,      4,      4,      5,      6,      7,      8,
       9,     10,     11,     11,     12,     12,     16,      3,
      34,     19,     20,     21,     21,     66,     66,     22,
      22,     23,     23,     24,     24,     25,     26,     26,
       8,     66,     68,     66,     72,     65,     65,     66,
      66,     66,      0,      0,      0,      0,      0,      0,
       0,      0,      4,     67,     67,     68,     69,     63,
       0,      0,      0,      0,      0,      0,      0,      0,
       0,      0,      0,      0,      8,     27,     28,     29,
      30,     31,     31,     32,     33,     33,      0,      0,
       0,      0,      0,      0,      0,      0,      4,     63,
      63,     63,     64,     63,      0,      0,      0,      0,
       0,      0,      0,      0,      0,      0,      0,      0,
};


const prog_uint8_t* const waveform_table[] = {
  wav_res_formant_sine,
  wav_res_formant_square,
  wav_res_sine,
  wav_res_bandlimited_square_0,
  wav_res_bandlimited_square_1,
  wav_res_bandlimited_square_2,
  wav_res_bandlimited_square_3,
  wav_res_bandlimited_square_4,
  wav_res_bandlimited_square_5,
  wav_res_sine,
  wav_res_bandlimited_saw_0,
  wav_res_bandlimited_saw_1,
  wav_res_bandlimited_saw_2,
  wav_res_bandlimited_saw_3,
  wav_res_bandlimited_saw_4,
  wav_res_bandlimited_saw_5,
  wav_res_sine,
  wav_res_bandlimited_triangle_0,
  wav_res_bandlimited_triangle_0,
  wav_res_bandlimited_triangle_0,
  wav_res_bandlimited_triangle_3,
  wav_res_bandlimited_triangle_4,
  wav_res_bandlimited_triangle_5,
  wav_res_sine,
  wav_res_vowel_data,
  wav_res_distortion,
  wav_res_lfo_waveforms,
  wav_res_env_expo,
  wav_res_waves,
  wav_res_wavetables,
};


}  // namespace ambika
