pichenettes/ambika/controller/storage.h

// Copyright 2011 Emilie Gillet.
//
// Author: Emilie Gillet (emilie.o.gillet@gmail.com)
//
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
// -----------------------------------------------------------------------------
//
// Patch storage and SysEx transfer.

#ifndef CONTROLLER_STORAGE_H_
#define CONTROLLER_STORAGE_H_

#include <avr/pgmspace.h>

#include "avrlib/base.h"

#include "avrlib/filesystem/filesystem.h"
#include "avrlib/filesystem/file.h"
#include "controller/voicecard_tx.h"

namespace ambika {

using avrlib::FilesystemStatus;

enum StorageObject {
  STORAGE_OBJECT_PATCH,
  STORAGE_OBJECT_SEQUENCE,
  STORAGE_OBJECT_PROGRAM,
  STORAGE_OBJECT_MULTI,
  STORAGE_OBJECT_PART,
};

enum SysExReceptionState {
  RECEIVING_HEADER = 0,
  RECEIVING_COMMAND = 1,
  RECEIVING_DATA = 2,
  RECEIVING_FOOTER = 3,
  RECEPTION_OK = 4,
  RECEPTION_ERROR = 5,
};

enum StorageDir {
  STORAGE_BANK,
  STORAGE_CLIPBOARD,
  STORAGE_PREVIOUS_CLIPBOARD,
  STORAGE_HISTORY
};

struct StorageLocation {
  StorageObject object;
  uint8_t part;
  uint8_t alias;
  uint8_t bank;
  uint8_t slot;
  char* name;

  inline uint16_t bank_slot() const {
    return (bank << 8) | slot;
  }
  
  inline uint8_t index() const {
    if (object == STORAGE_OBJECT_MULTI) {
      return kNumVoices * 3;
    } else {
      return part * 3 + object;
    }
  }
};

typedef void (*ObjectFn)(const StorageLocation& location);

static const uint16_t kFsInitTimeout = 750;

class Storage {
 public:
  Storage() { }
  
  static void Init();
  static FilesystemStatus InitFilesystem() {
    scoped_resource<SdCardSession> session;
    return fs_.Init(kFsInitTimeout);
  }

  static inline void Tick() {
    fs_.Tick();
  }

  static uint8_t Checksum(const void* data, uint8_t size);
  
  static void SysExSend(const StorageLocation& location) {
    ForEachObject(location, &SysExSendObject);
  }
  
  static FilesystemStatus Snapshot(const StorageLocation& location);
  static FilesystemStatus PreviousVersion(const StorageLocation& location);
  static FilesystemStatus NextVersion(const StorageLocation& location);
  
  static FilesystemStatus Copy(const StorageLocation& location) {
    return Save(STORAGE_CLIPBOARD, location);
  }
  static FilesystemStatus Paste(const StorageLocation location) {
    Snapshot(location);
    return Load(STORAGE_CLIPBOARD, location, 1);
  }
  static FilesystemStatus Swap(const StorageLocation location) {
    Snapshot(location);
    Save(STORAGE_CLIPBOARD, location);
    return Load(STORAGE_PREVIOUS_CLIPBOARD, location, 1);
  }
  static FilesystemStatus Load(const StorageLocation location) {
    if (has_user_changes(location)) {
      Snapshot(location);
    }
    return Load(STORAGE_BANK, location, 1);
  }
  
  static FilesystemStatus LoadName(const StorageLocation location) {
    return Load(STORAGE_BANK, location, 0);
  }
  
  static FilesystemStatus Save(const StorageLocation& location) {
    return Save(STORAGE_BANK, location);
  }
  
  static FilesystemStatus Mkfs() {
    scoped_resource<SdCardSession> session;
    InvalidatePendingSysExTransfer();
    return fs_.Mkfs();
  }
  
  static uint32_t GetFreeSpace() {
    scoped_resource<SdCardSession> session;
    InvalidatePendingSysExTransfer();
    return fs_.GetFreeSpace();
  }
  
  static uint8_t FileExists(const prog_char* name) {
    return FileExists(name, 0);
  }
  static uint8_t FileExists(const prog_char* name, char variable);

  static FilesystemStatus SpiCopy(
      uint8_t voice_id,
      const prog_char* name,
      char variable,
      uint8_t page_size_nibbles);
  
  static uint16_t GetType() {
    return fs_.GetType();
  }
  
  static void SysExReceive(uint8_t byte);
  
  static inline uint8_t sysex_rx_state() {
    return sysex_rx_state_;
  }
  
  static inline uint8_t version(const StorageLocation& location) {
    return version_[location.index()];
  }

  static uint8_t has_user_changes(const StorageLocation& location);

  static void WriteMultiToEeprom();
  static uint8_t LoadMultiFromEeprom();

 private:
  static void InvalidatePendingSysExTransfer();
  
  static void Expand(const prog_char* name, char variable);
  
  static FilesystemStatus Save(
      StorageDir type,
      const StorageLocation& location);

  static FilesystemStatus Load(
      StorageDir type,
      const StorageLocation& location,
      uint8_t load_contents);

  static char* GetFileName(StorageDir type, const StorageLocation& location);

  static uint16_t riff_size(const StorageLocation& location);
  static uint8_t object_size(const StorageLocation& location);
  static const uint8_t* object_data(const StorageLocation& location);
  static uint8_t* mutable_object_data(const StorageLocation& location);
  
  static void ForEachObject(const StorageLocation& source, ObjectFn object_fn);
  
  static void ReadObject(const StorageLocation& location);
  static void SysExSendObject(const StorageLocation& location);
  static void SysExSendRaw(uint8_t, uint8_t, const uint8_t*, uint8_t, bool);
  static void RIFFWriteObject(const StorageLocation& location);
  static void TouchObject(const StorageLocation& location);

  static void SysExParseCommand();
  static void SysExAcceptCommand();
  
  static void EepromWrite(const void* data, uint8_t size, uint16_t* offset);
  static uint8_t EepromRead(void* data, uint8_t size, uint16_t* offset);
  
  static uint8_t* buffer_;
  
  static uint16_t sysex_rx_bytes_received_;
  static uint16_t sysex_rx_expected_size_;
  static uint8_t sysex_rx_state_;
  static uint8_t sysex_rx_checksum_;
  static uint8_t sysex_rx_command_[2];
  
  static char tmp_buffer_[64];
  
  static uint8_t version_[kNumVoices * 3 + 1];
  
  static avrlib::Filesystem fs_;
  static avrlib::File file_;
  
  DISALLOW_COPY_AND_ASSIGN(Storage);
};

extern Storage storage;

}  // namespace ambika

#endif  // CONTROLLER_STORAGE_H_
