pichenettes/ambika/controller/voice_allocator.cc

// Copyright 2011 Emilie Gillet.
//
// Author: Emilie Gillet (emilie.o.gillet@gmail.com)
//
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
// -----------------------------------------------------------------------------
//
// Polyphonic voice allocator.

#include "controller/voice_allocator.h"

#include <string.h>

namespace ambika {
  
void VoiceAllocator::Clear() {
  ClearNotes();
  for (uint8_t i = 0; i < size_; ++i) {
    lru_[i] = size_ - i - 1;
  }
}

void VoiceAllocator::ClearNotes() {
  memset(pool_, 0, size_);
}

uint8_t VoiceAllocator::NoteOn(uint8_t note) {
  if (size_ == 0) {
    return 0xff;
  }
  
  uint8_t voice;
  
  if (cyclic_allocator_ == 0xff) {
    // First, check if there is a voice currently playing this note. In this case
    // This voice will be responsible for retriggering this note.
    // Hint: if you're more into string instruments than keyboard instruments,
    // you can safely comment those lines.
    voice = Find(note);
  
    // Then, try to find the least recently touched, currently inactive voice.
    if (voice == 0xff) {
      for (uint8_t i = 0; i < size_; ++i) {
        if (lru_[i] < size_ && !(pool_[lru_[i]] & 0x80)) {
          voice = lru_[i];
        }
      }
    }
    // If all voices are active, use the least recently played note.
    if (voice == 0xff) {
      for (uint8_t i = 0; i < size_; ++i) {
        if (lru_[i] < size_) {
          voice = lru_[i];
        }
      }
    }
  } else {
    ++cyclic_allocator_;
    if (cyclic_allocator_ >= size_) {
      cyclic_allocator_ = 0;
    }
    voice = cyclic_allocator_;
  }
  
  pool_[voice] = 0x80 | note;
  Touch(voice);
  return voice;
}

uint8_t VoiceAllocator::Find(uint8_t note) const {
  for (uint8_t i = 0; i < size_; ++i) {
    if ((pool_[i] & 0x7f) == note) {
      return i;
    }
  }
  return 0xff;
}

uint8_t VoiceAllocator::FindActive(uint8_t note) const {
  for (uint8_t i = 0; i < size_; ++i) {
    if ((pool_[i] & 0x7f) == note && (pool_[i] & 0x80)) {
      return i;
    }
  }
  return 0xff;
}

uint8_t VoiceAllocator::NoteOff(uint8_t note) {
  uint8_t voice = Find(note);
  if (cyclic_allocator_ == 0xff) {
    if (voice != 0xff) {
      pool_[voice] &= 0x7f;
      Touch(voice);
    }
  } else {
    if (voice != 0xff) {
      pool_[voice] = 0xff;
    }
  }
  return voice;
}

void VoiceAllocator::Touch(uint8_t voice) {
  int8_t source = size_ - 1;
  int8_t destination = size_ - 1;
  while (source >= 0) {
    if (lru_[source] != voice) {
      lru_[destination--] = lru_[source];
    }
    --source;
  }
  lru_[0] = voice;
}

}  // namespace ambika
