pichenettes/ambika/voicecard/oscillator.h

// Copyright 2011 Emilie Gillet.
//
// Author: Emilie Gillet (emilie.o.gillet@gmail.com)
//
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
// -----------------------------------------------------------------------------
//
// Oscillators. Note that the code of each oscillator is duplicated/specialized,
// for a noticeable performance boost.

#ifndef VOICECARD_OSCILLATOR_H_
#define VOICECARD_OSCILLATOR_H_

#include "avrlib/op.h"
#include "avrlib/random.h"

#include "common/patch.h"

#include "voicecard/resources.h"

using namespace avrlib;

namespace ambika {

static inline uint8_t ReadSample(
    const prog_uint8_t* table,
    uint16_t phase) __attribute__((always_inline));
static inline uint8_t ReadSample(
    const prog_uint8_t* table,
    uint16_t phase) {
  return ResourcesManager::Lookup<uint8_t, uint8_t>(table, phase >> 8);
}

static inline uint8_t InterpolateTwoTables(
    const prog_uint8_t* table_a, const prog_uint8_t* table_b,
    uint16_t phase, uint8_t gain_a, uint8_t gain_b) {
  return U8Mix(
      InterpolateSample(table_a, phase),
      InterpolateSample(table_b, phase),
      gain_a, gain_b);
}

static const uint8_t kNumZonesFullSampleRate = 6;
static const uint8_t kNumZonesHalfSampleRate = 5;

struct VowelSynthesizerState {
  uint16_t formant_increment[3];
  uint16_t formant_phase[3];
  uint8_t formant_amplitude[3];
  uint8_t noise_modulation;
  uint8_t update;  // Update only every kVowelControlRateDecimation-th call.
};

struct FilteredNoiseState {
  uint8_t lp_noise_sample;
  uint16_t rng_state;
  uint16_t rng_reset_value;
};

struct QuadSawPadState {
  uint16_t phase[3];
};

union OscillatorState {
  VowelSynthesizerState vw;
  FilteredNoiseState no;
  QuadSawPadState qs;
  uint16_t secondary_phase;
};

typedef void (*OscRenderFn)(uint8_t* buffer);

class Oscillator {
 public:
  typedef void (Oscillator::*RenderFn)(uint8_t*);
   
  Oscillator() { }
  ~Oscillator() { }

  inline void Reset() {
    data_.no.rng_reset_value = Random::GetByte() + 1;
  }

  inline void Render(
      uint8_t shape,
      uint8_t note,
      uint24_t increment,
      uint8_t* sync_input,
      uint8_t* sync_output,
      uint8_t* buffer) {
    shape_ = shape;
    note_ = note;
    phase_increment_ = increment;
    sync_input_ = sync_input;
    sync_output_ = sync_output;
    // A hack: when pulse width is set to 0, use a simple wavetable.
    if (shape_ == WAVEFORM_SQUARE) {
      if (parameter_ == 0) {
        RenderSimpleWavetable(buffer);
      } else {
        RenderBandlimitedPwm(buffer);
      }
    } else {
      RenderFn fn;
      
      uint8_t index = shape_ >= WAVEFORM_WAVETABLE_1
          ? WAVEFORM_WAVETABLE_1
          : shape_;
      ResourcesManager::Load(fn_table_, index, &fn);
      if (shape_ == WAVEFORM_WAVEQUENCE) {
        fn = &Oscillator::RenderWavequence;
      }
      (this->*fn)(buffer);
    }
  }
  
  inline void set_parameter(uint8_t parameter) {
    parameter_ = parameter;
  }
  
  inline void set_fm_parameter(uint8_t fm_parameter) {
    fm_parameter_ = fm_parameter;
  }
  
 private:
  // Current phase of the oscillator.
  uint24_t phase_;

  // Phase increment (and phase increment x 2, for low-sr oscillators).
  uint24_t phase_increment_;

  // Copy of the shape used by this oscillator. When changing this, you
  // should also update the Update/Render pointers.
  uint8_t shape_;

  // Current value of the oscillator parameter.
  uint8_t parameter_;
  uint8_t fm_parameter_;
  uint8_t note_;

  // Union of state data used by each algorithm.
  OscillatorState data_;

  // Pointer to the render function.
  static const RenderFn fn_table_[];
  
  // A flag set to true when sync is enabled ; and a table to record the
  // position of phrase wraps
  uint8_t* sync_input_;
  uint8_t* sync_output_;
  
  void RenderSilence(uint8_t* buffer);
  void RenderBandlimitedPwm(uint8_t* buffer);
  void RenderSimpleWavetable(uint8_t* buffer);
  void RenderCzSaw(uint8_t* buffer);
  void RenderCzResoSaw(uint8_t* buffer);
  void RenderCzResoPulse(uint8_t* buffer);
  void RenderCzResoTri(uint8_t* buffer);
  void RenderFm(uint8_t* buffer);
  void Render8BitLand(uint8_t* buffer);
  void RenderVowel(uint8_t* buffer);
  void RenderDirtyPwm(uint8_t* buffer);
  void RenderQuadSawPad(uint8_t* buffer);
  void RenderFilteredNoise(uint8_t* buffer);
  void RenderInterpolatedWavetable(uint8_t* buffer);
  void RenderWavequence(uint8_t* buffer);
  
  DISALLOW_COPY_AND_ASSIGN(Oscillator);
};

}  // namespace ambika

#endif  // VOICECARD_OSCILLATOR_H_
